AC8L/QMX_Plus_Autotuner_Internal_Battery_Speaker/ABS_ATU_Audio_Amp_PCB/ABS_ATU_Audio_Amp_PCB_v2.0 - Front.jpg

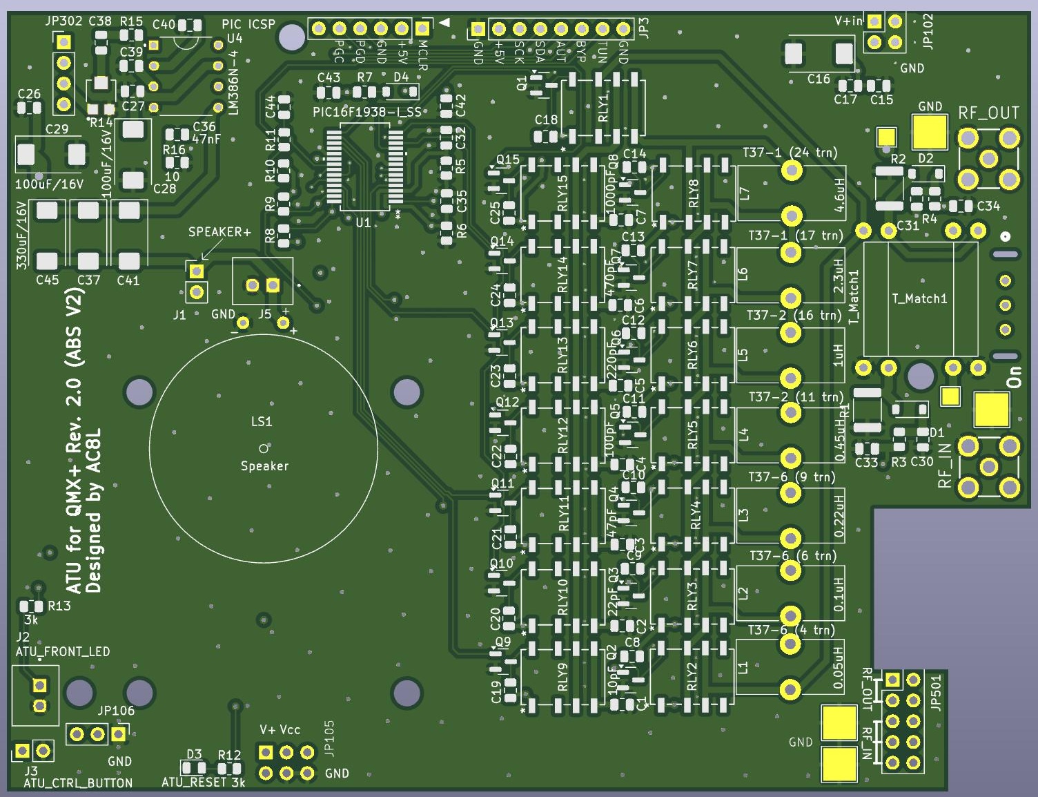
ABS_ATU_Audio_Amp_PCB/ABS_ATU_Audio_Amp_PCB_v2.0 - Front.jpg
