AC8L/QMX_Plus_Autotuner_Internal_Battery_Speaker/ABS_Rear_Panel_Mod_For_Battery_V2/ABS Rear Panel Mod - SMA v2.2/ABS Rear Panel Mod - SMA v2.2  - Front.png

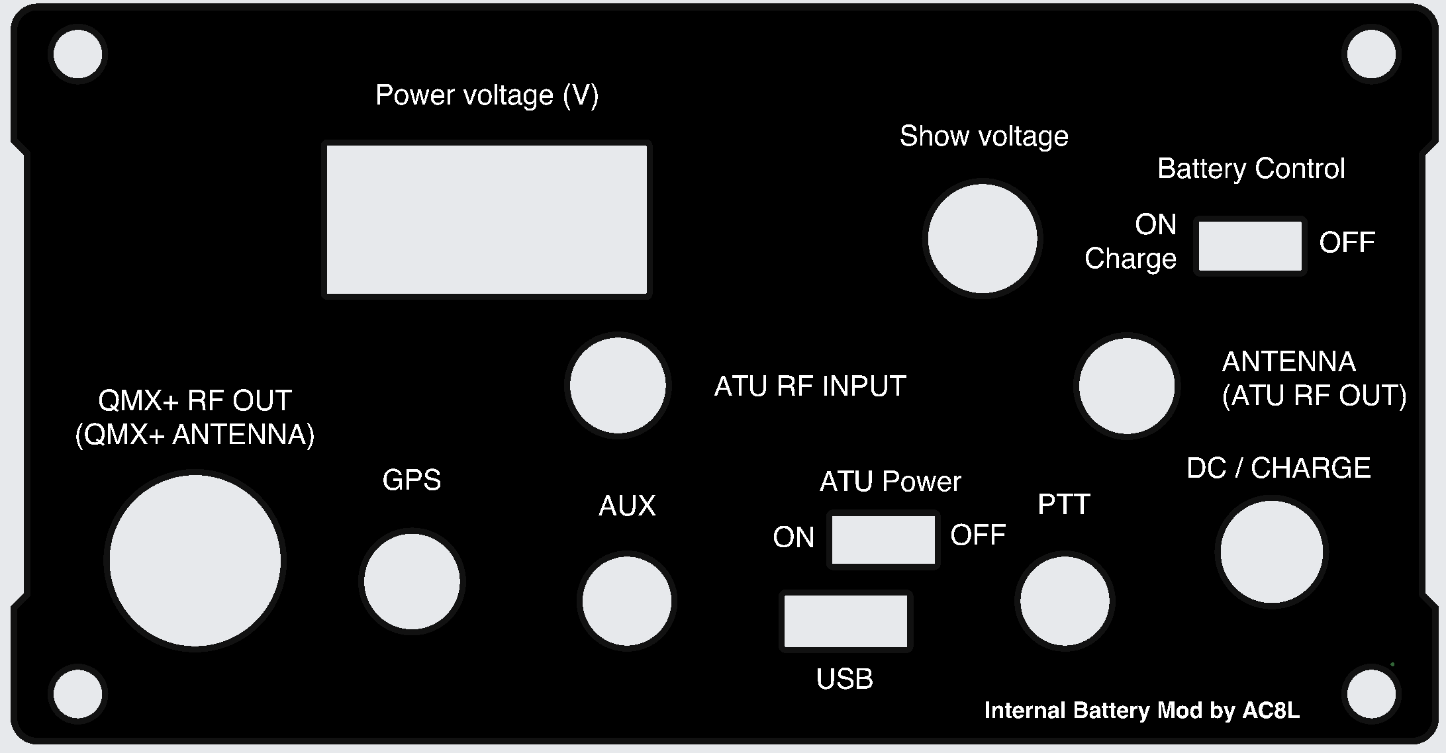
ABS_Rear_Panel_Mod_For_Battery_V2/ABS Rear Panel Mod - SMA v2.2/ABS Rear Panel Mod - SMA v2.2 - Front.png
