AC8L/QMX_Plus_Autotuner_Internal_Battery_Speaker/ABS_Battery_Speaker_PCB/3D Prints/ABS V2 Voltmeter Mounting Bracket.png

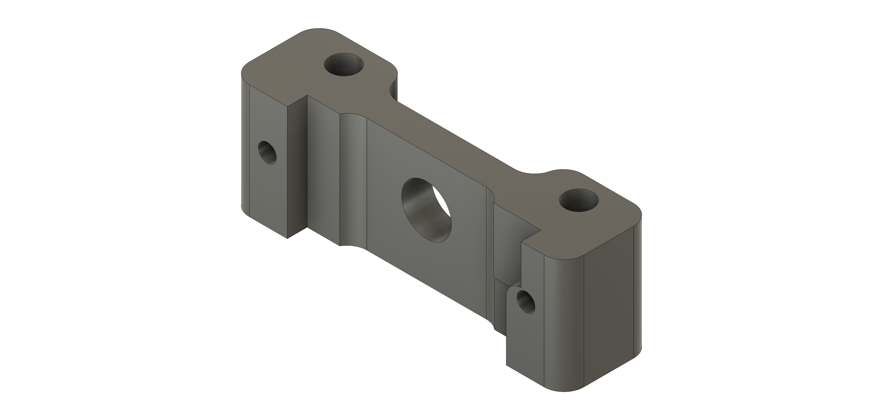
ABS_Battery_Speaker_PCB/3D Prints/ABS V2 Voltmeter Mounting Bracket.png
