AC8L/QMX_Plus_Autotuner_Internal_Battery_Speaker/ABS_Rear_Panel_Mod_For_Battery_V2/ABS Rear Panel Mod - No SMA v2.2/3D Prints/ABS Back Panel with Battery Slide Switch - V.2.2 - NO SMA.png

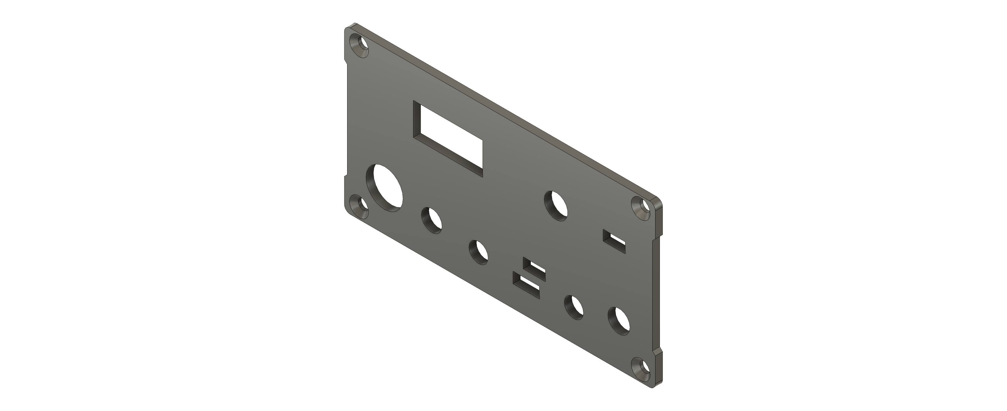
ABS_Rear_Panel_Mod_For_Battery_V2/ABS Rear Panel Mod - No SMA v2.2/3D Prints/ABS Back Panel with Battery Slide Switch - V.2.2 - NO SMA.png
